OnionIoT/Omega2-Pro/Images/OM-O2PRO-0-top-1.jpg

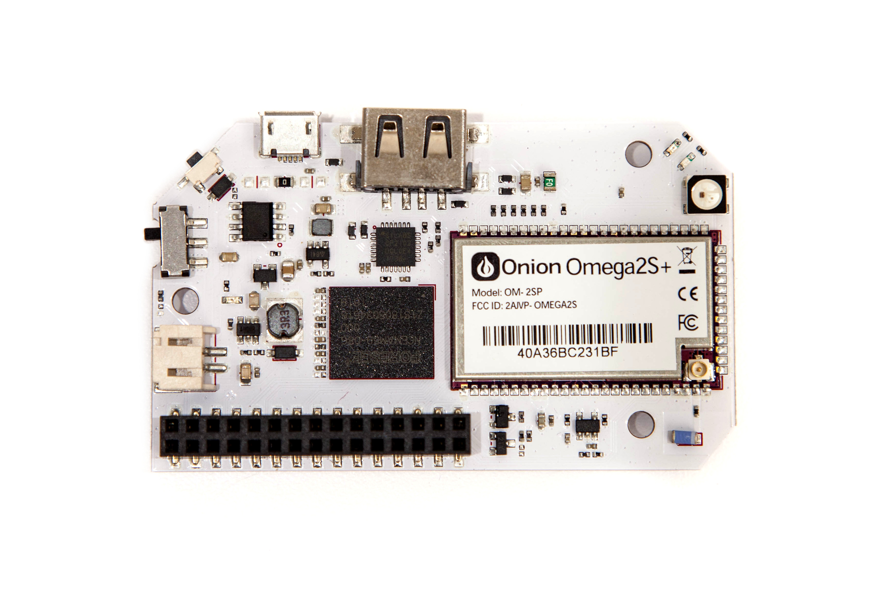
Images/OM-O2PRO-0-top-1.jpg
