OnionIoT/Omega2-Pro/Images/OM-O2PRO-1-bottom-1.jpg

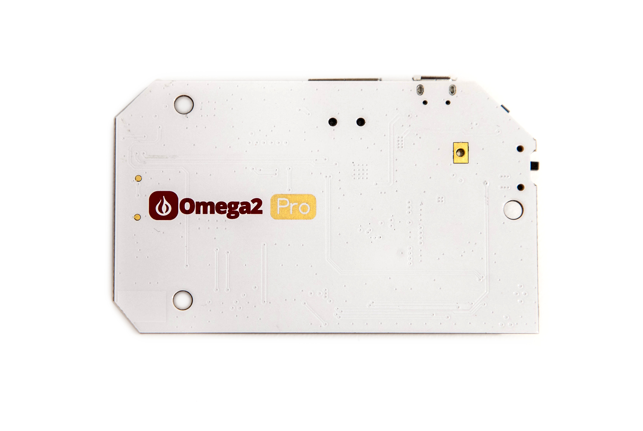
Images/OM-O2PRO-1-bottom-1.jpg
