OnionIoT/Omega2-Pro/Images/OM-O2PRO-2-side-2.jpg

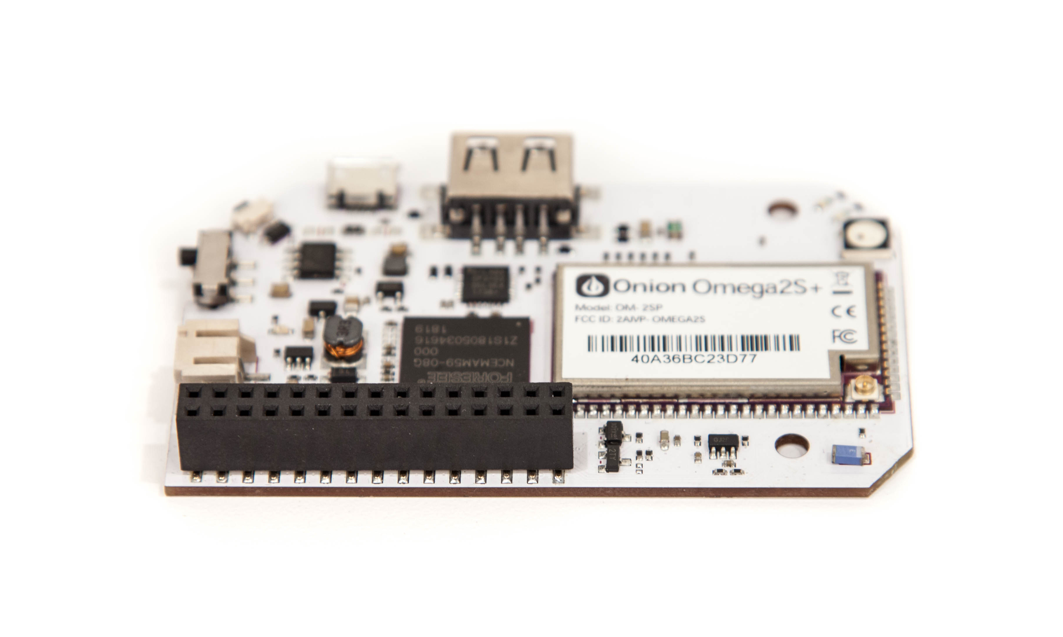
Images/OM-O2PRO-2-side-2.jpg
