OnionIoT/Omega2-Pro/Images/OM-O2PRO-4-iso-1.jpg

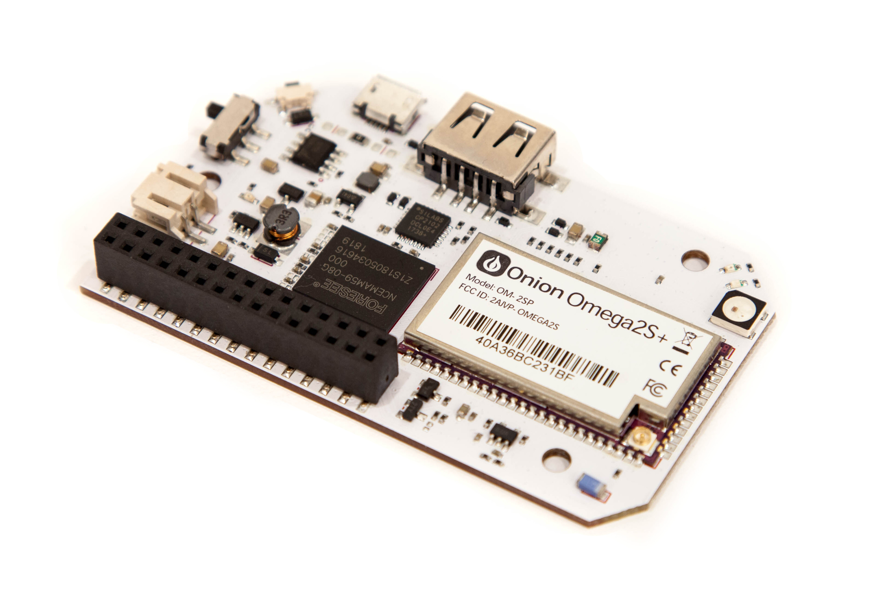
Images/OM-O2PRO-4-iso-1.jpg
