OnionIoT/Omega2-Pro/Images/OM-O2PRO-6-multiple-1.jpg

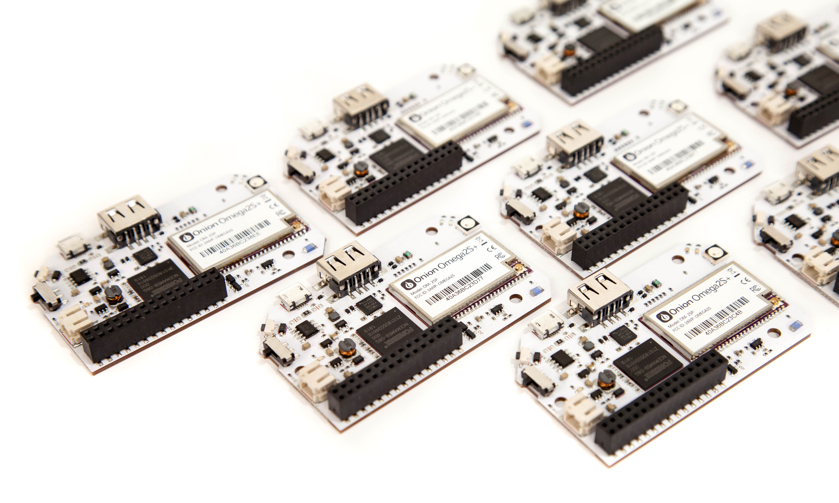
Images/OM-O2PRO-6-multiple-1.jpg
