OnionIoT/Omega2-Pro/Images/OM-O2PRO-6-multiple-close.jpg

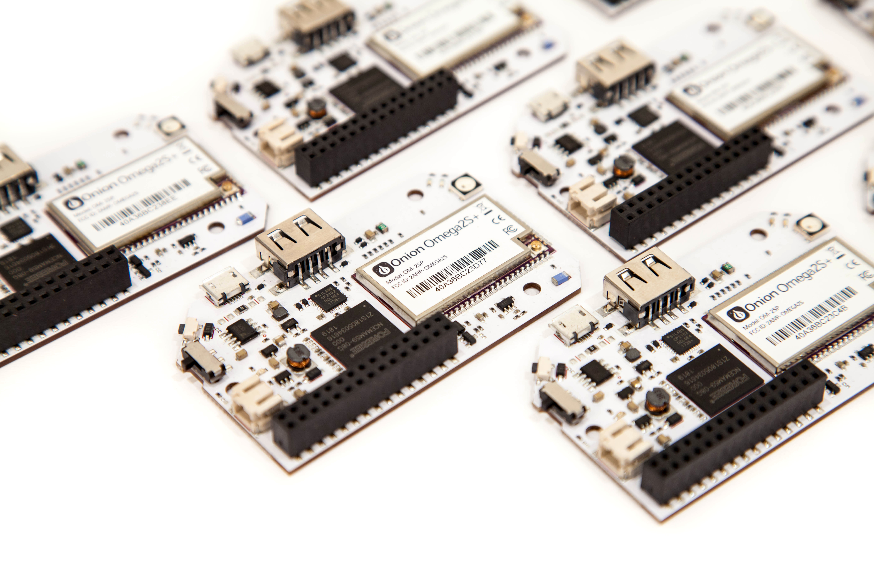
Images/OM-O2PRO-6-multiple-close.jpg
