OnionIoT/Omega2-Pro/Images/OM-O2PRO-7-box-2.jpg

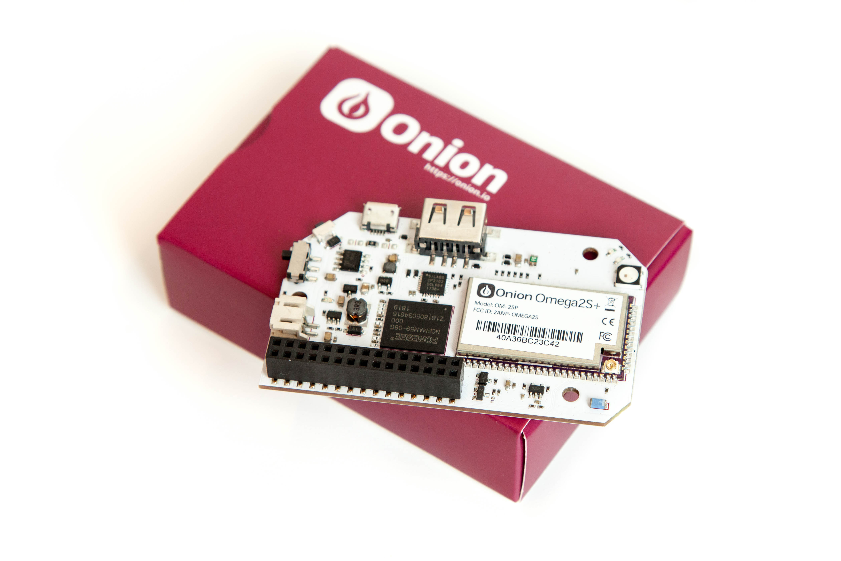
Images/OM-O2PRO-7-box-2.jpg
