OnionIoT/Omega2-Pro/Images/OM-O2PRO-7-box-3.jpg

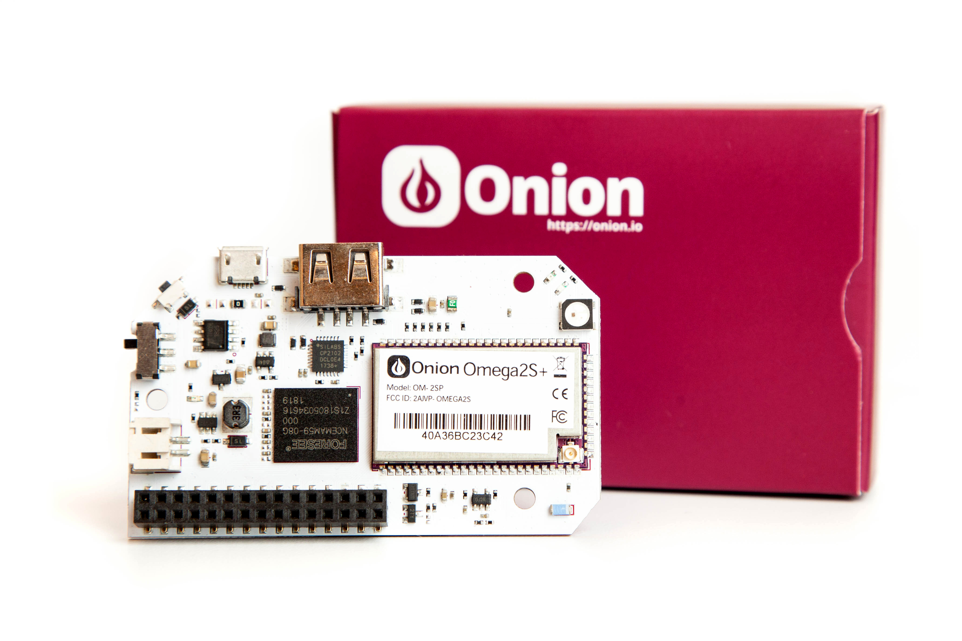
Images/OM-O2PRO-7-box-3.jpg
