OnionIoT/Omega2-Pro/Images/OM-O2PRO-7-box-5.jpg

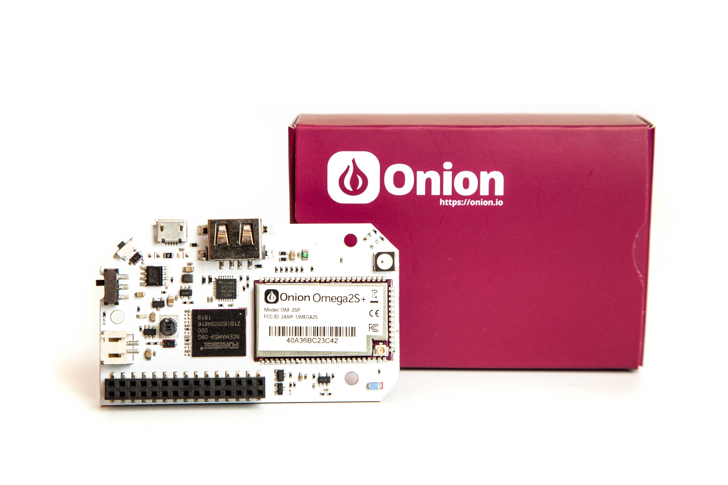
Images/OM-O2PRO-7-box-5.jpg
